BasementEngineering/lekey/CAD/Controller/Bottom.stl

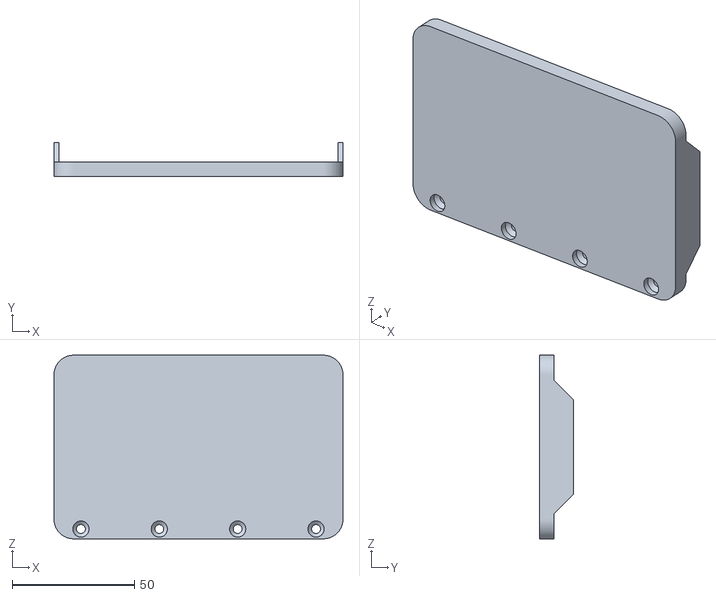
[picture p24: CAD file, 2025-07-02]
CAD/Controller/Bottom.stl
118.0 x 14.0 x 75.0
